bambaF01/Mesure-Tension-cable/Dossier_kicad/alim/alim.kicad_pcb

## KiCad design schematic/CPU_board.kicad_sch

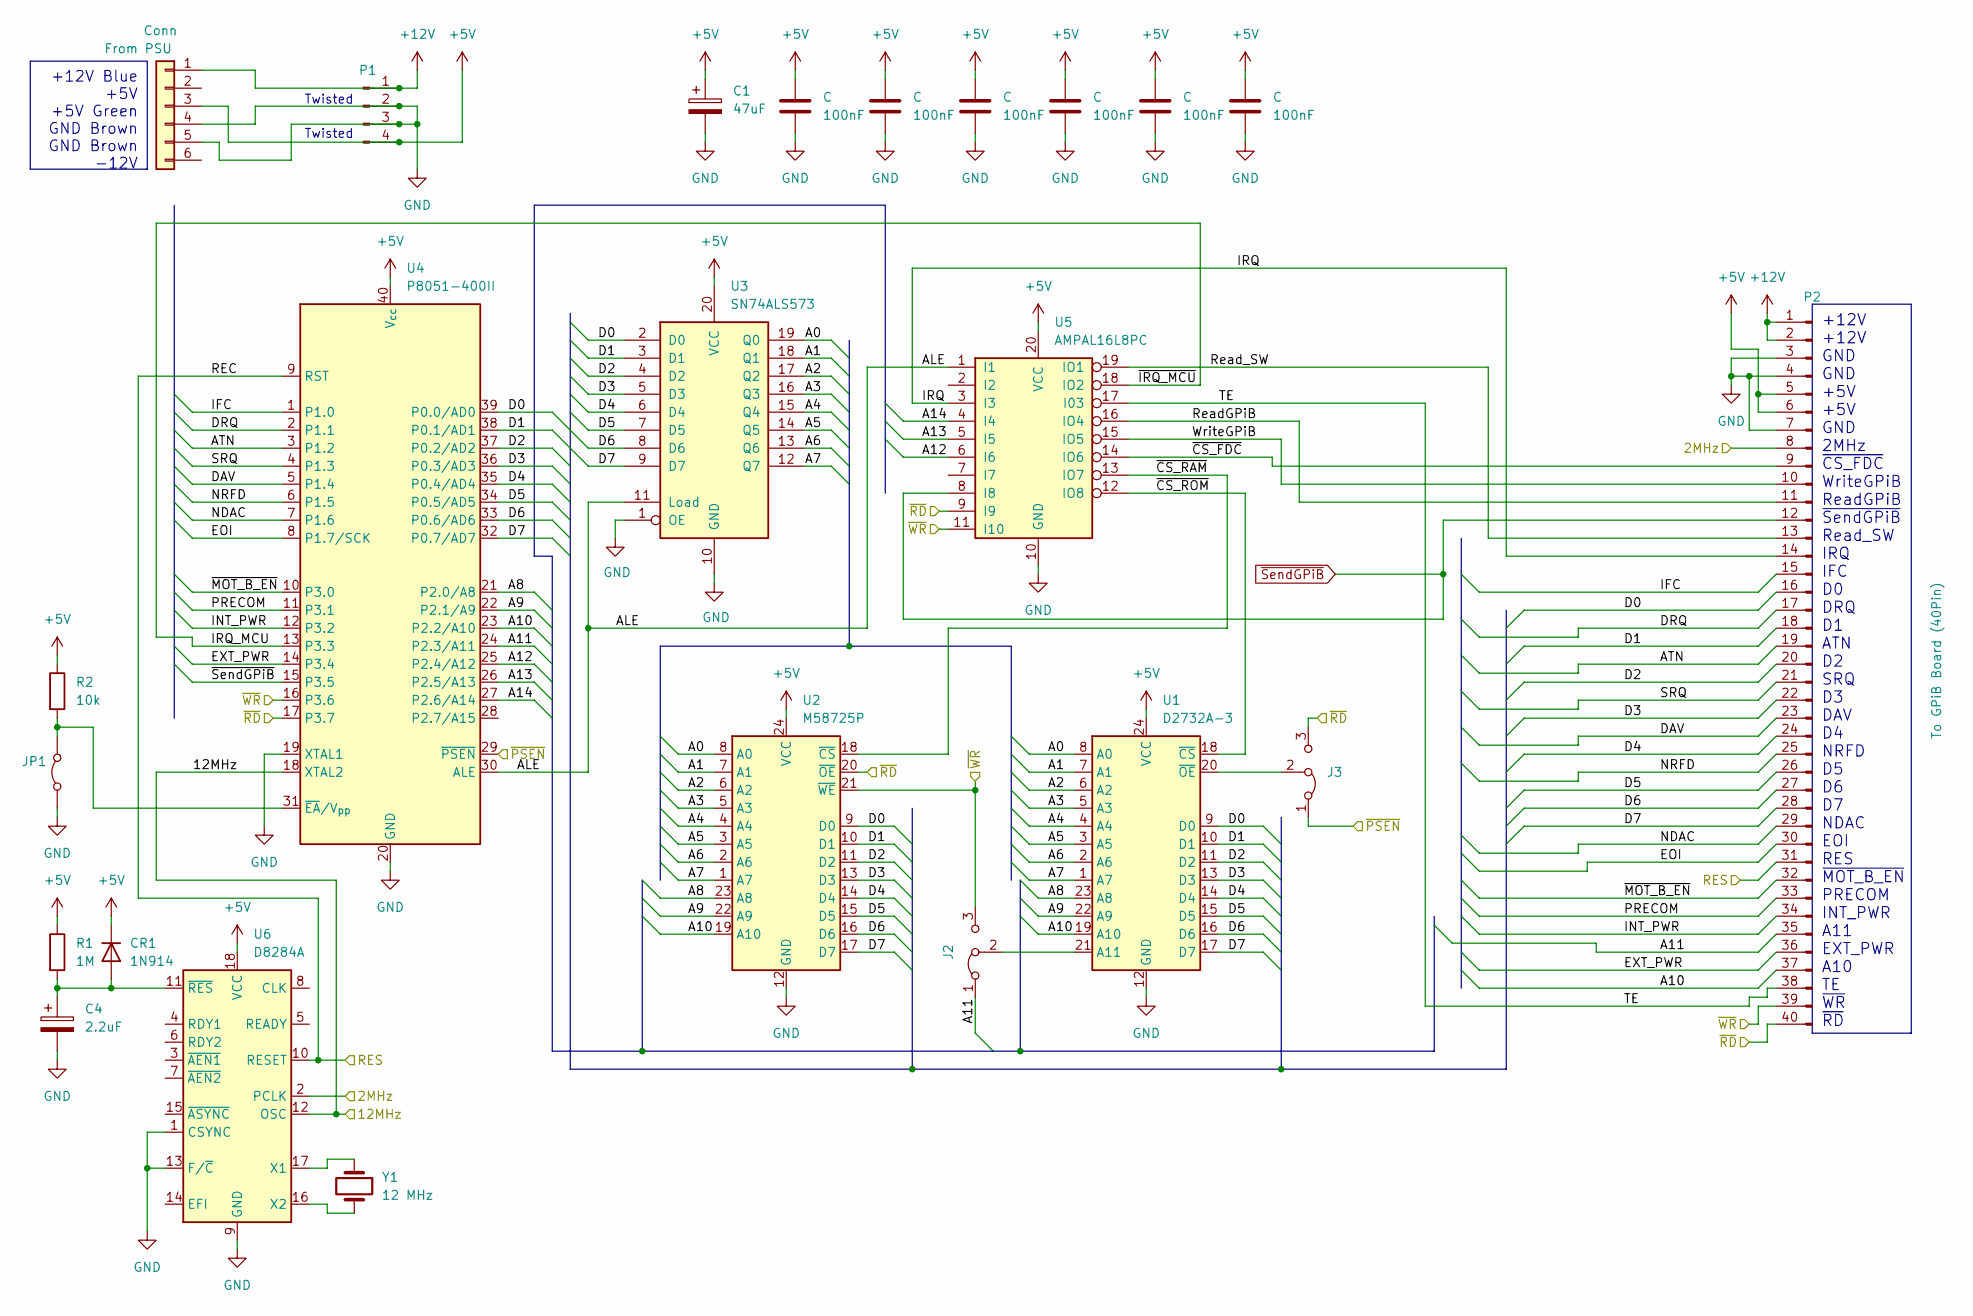
[picture p7: schematic CPU_board.kicad_sch]

Parts:
C: 100nF; C_Disc_D4.3mm_W1.9mm_P5.00mm
C1: 47uF; CP_Axial_L21.0mm_D8.0mm_P28.00mm_Horizontal; Voltage 10V
C4: 2.2uF; C_Disc_D5.0mm_W2.5mm_P2.50mm; Voltage 25V
CR1: 1N914; D_DO-35_SOD27_P10.16mm_Horizontal
Conn: From PSU
J2, J3: Jumper_3_Bridged12
JP1: (no value)
P1: Conn_01x04_Pin
P2: To GPiB Board (40Pin)
R1: 1M; R_Axial_DIN0309_L9.0mm_D3.2mm_P12.70mm_Horizontal
R2: 10k; R_Axial_DIN0309_L9.0mm_D3.2mm_P12.70mm_Horizontal
U1: D2732A-3; DIP-24_W15.24mm
U2: M58725P; DIP-24_W15.24mm
U3: SN74ALS573; DIP-20_W7.62mm
U4: P8051-400II; DIP-40_W15.24mm
U5: AMPAL16L8PC
U6: D8284A; DIP-18_W7.62mm
Y1: 12 MHz; Crystal_HC49-U_Horizontal

Connections:
2MHz: P2.8, U6.2 (PCLK)
12MHz: U4.18 (XTAL2), U6.12 (OSC)
+5V: C.1, C1.1, CR1.1 (K), Conn.3, P1.4, P2.5, P2.6, R1.1, R2.1, U1.24 (VCC), U2.24 (VCC), U3.20 (VCC), U4.40 (V_{cc}), U5.20 (VCC), U6.18 (VCC)
+12V: Conn.1, P1.1, P2.1, P2.2
A0: U1.8 (A0), U2.8 (A0), U3.19 (Q0)
A1: U1.7 (A1), U2.7 (A1), U3.18 (Q1)
A2: U1.6 (A2), U2.6 (A2), U3.17 (Q2)
A3: U1.5 (A3), U2.5 (A3), U3.16 (Q3)
A4: U1.4 (A4), U2.4 (A4), U3.15 (Q4)
A5: U1.3 (A5), U2.3 (A5), U3.14 (Q5)
A6: U1.2 (A6), U2.2 (A6), U3.13 (Q6)
A7: U1.1 (A7), U2.1 (A7), U3.12 (Q7)
A8: U1.23 (A8), U2.23 (A8), U4.21 (P2.0/A8)
A9: U1.22 (A9), U2.22 (A9), U4.22 (P2.1/A9)
A10: U1.19 (A10), U2.19 (A10), U4.23 (P2.2/A10)
A11: J2.1 (A), U4.24 (P2.3/A11)
A12: U4.25 (P2.4/A12), U5.6 (I6)
A13: U4.26 (P2.5/A13), U5.5 (I5)
A14: U4.27 (P2.6/A14), U5.4 (I4)
ALE: U3.11 (Load), U4.30 (ALE), U5.1 (I1)
ATN: U4.3 (P1.2)
D0: U1.9 (D0), U2.9 (D0), U3.2 (D0), U4.39 (P0.0/AD0)
D1: U1.10 (D1), U2.10 (D1), U3.3 (D1), U4.38 (P0.1/AD1)
D2: U1.11 (D2), U2.11 (D2), U3.4 (D2), U4.37 (P0.2/AD2)
D3: U1.13 (D3), U2.13 (D3), U3.5 (D3), U4.36 (P0.3/AD3)
D4: U1.14 (D4), U2.14 (D4), U3.6 (D4), U4.35 (P0.4/AD4)
D5: U1.15 (D5), U2.15 (D5), U3.7 (D5), U4.34 (P0.5/AD5)
D6: U1.16 (D6), U2.16 (D6), U3.8 (D6), U4.33 (P0.6/AD6)
D7: U1.17 (D7), U2.17 (D7), U3.9 (D7), U4.32 (P0.7/AD7)
DAV: U4.5 (P1.4)
DRQ: U4.2 (P1.1)
EOI: U4.8 (P1.7/SCK)
EXT_PWR: U4.14 (P3.4)
GND: C.2, C1.2, C4.2, Conn.4, Conn.5, JP1.1 (A), P1.2, P1.3, P2.3, P2.4, P2.7, U1.12 (GND), U2.12 (GND), U3.1 (OE), U3.10 (GND), U4.19 (XTAL1), U4.20 (GND), U5.10 (GND), U6.1 (CSYNC), U6.9 (GND), U6.13 (F/~C)
IFC: U4.1 (P1.0)
INT_PWR: U4.12 (P3.2)
IRQ: P2.14, U5.3 (I3)
IRQ_MCU: U4.13 (P3.3), U5.18 (IO2)
NDAC: U4.7 (P1.6)
NRFD: U4.6 (P1.5)
unnamed: C4.1, CR1.2 (A), R1.2, U6.11 (~RES)
unnamed: J2.2 (C), U1.21 (A11)
unnamed: J3.2 (C), U1.20 (~OE)
unnamed: JP1.2 (B), R2.2, U4.31 (~EA/V_{pp})
unnamed: U6.16 (X2), Y1.2
unnamed: U6.17 (X1), Y1.1
PRECOM: U4.11 (P3.1)
REC: U4.9 (RST), U6.10 (RESET)
ReadGPiB: P2.11, U5.16 (IO4)
Read_SW: P2.13, U5.19 (IO1)
SRQ: U4.4 (P1.3)
WriteGPiB: P2.10, U5.15 (IO5)
~CS_FDC: P2.9, U5.14 (IO6)
~CS_RAM: U2.18 (~CS), U5.13 (IO7)
~CS_ROM: U1.18 (~CS), U5.12 (IO8)
~MOT_B_EN: U4.10 (P3.0)
~PSEN: J3.1 (A), U4.29 (~PSEN)
~RD: J3.3 (B), P2.40, U2.20 (~OE), U4.17 (P3.7), U5.9 (I9)
~SendGPiB: P2.12, U4.15 (P3.5), U5.8 (I8)
~WR: J2.3 (B), P2.39, U2.21 (~WE), U4.16 (P3.6), U5.11 (I10)
ТЕ: P2.38, U5.17 (I03)

Notes on the sheet:
+12V +12V GND GND +5V +5V GND 2MHz ~{CS_FDC} WriteGPiB ReadGPiB ~{SendGPiB} Read_SW IRQ IFC D0 DRQ D1 ATN D2 SRQ D3 DAV D4 NRFD D5 D6 D7 NDAC EOI RES ~{MOT_B_EN} PRECOM INT_PWR A11 EXT_PWR A10 ТЕ ~{WR} ~{RD}
+12V Blue +5V +5V Green GND Brown GND Brown -12V
Twisted
