bambaF01/Mesure-Tension-cable/Dossier_kicad/alim/alim.kicad_pcb

## KiCad design schematic/GPiB_Board.kicad_sch

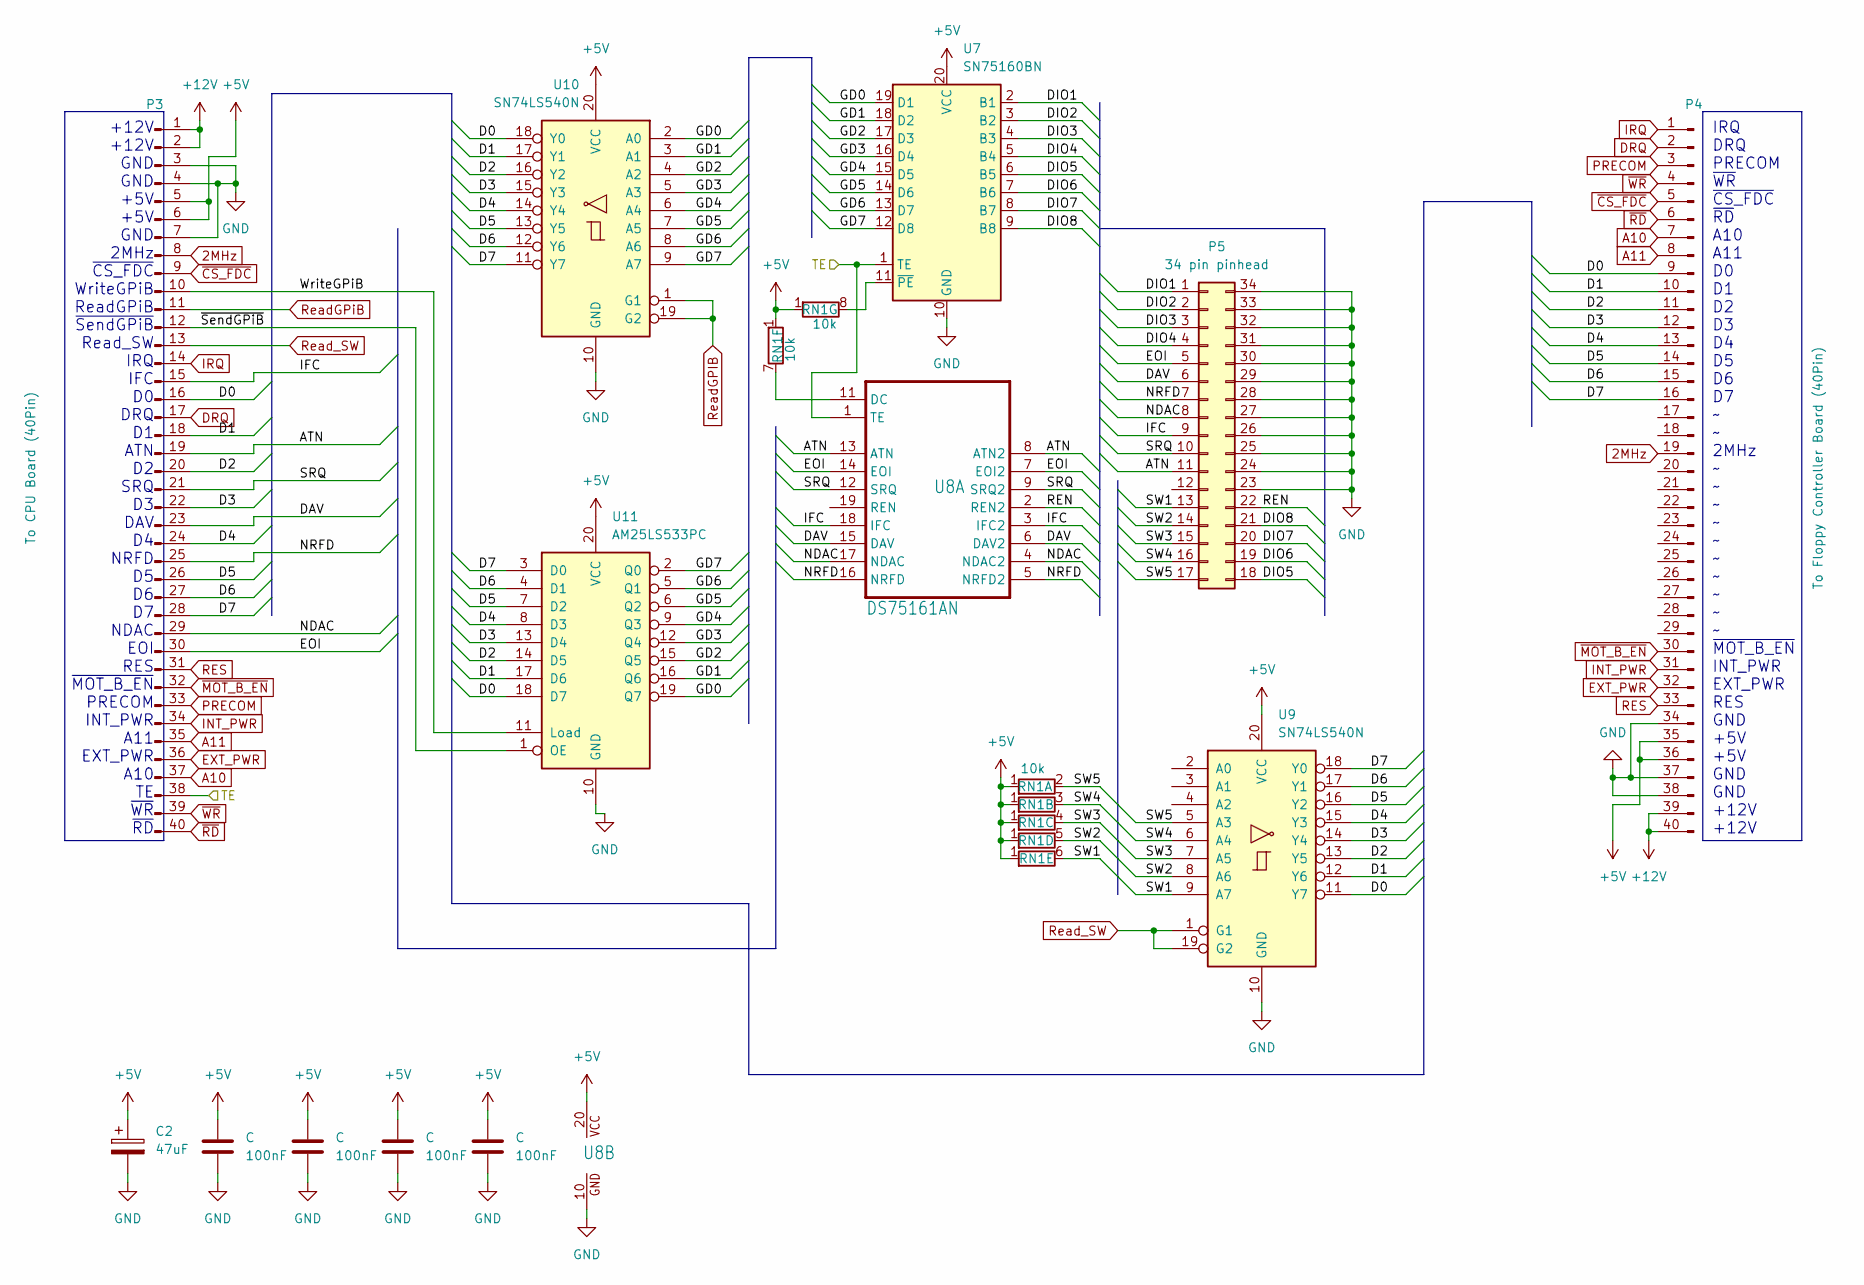
[picture p9: schematic GPiB_Board.kicad_sch]

Parts:
C: 100nF; C_Disc_D4.3mm_W1.9mm_P5.00mm
C2: 47uF; CP_Axial_L21.0mm_D8.0mm_P28.00mm_Horizontal; Voltage 10V
P3: To CPU Board (40Pin)
P4: To Floppy Controller Board (40Pin)
P5: 34 pin pinhead
RN1: 10k; R_Array_SIP8
U7: SN75160BN; DIP-20_W7.62mm
U8: 75161P; DIL20
U9, U10: SN74LS540N
U11: AM25LS533PC

Connections:
2MHz: P3.8, P4.19
+5V: C.1, C2.1, P3.5, P3.6, P4.35, P4.36, RN1.1 (R1), U7.20 (VCC), U8.20 (VCC), U9.20 (VCC), U10.20 (VCC), U11.20 (VCC)
+12V: P3.1, P3.2, P4.39, P4.40
A10: P3.37, P4.7
A11: P3.35, P4.8
ATN: P3.19, P5.11, U8.8 (ATN2), U8.13 (ATN)
D0: P3.16, P4.9, U9.11 (Y7), U10.18 (Y0), U11.18 (D7)
D1: P3.18, P4.10, U9.12 (Y6), U10.17 (Y1), U11.17 (D6)
D2: P3.20, P4.11, U9.13 (Y5), U10.16 (Y2), U11.14 (D5)
D3: P3.22, P4.12, U9.14 (Y4), U10.15 (Y3), U11.13 (D4)
D4: P3.24, P4.13, U9.15 (Y3), U10.14 (Y4), U11.8 (D3)
D5: P3.26, P4.14, U9.16 (Y2), U10.13 (Y5), U11.7 (D2)
D6: P3.27, P4.15, U9.17 (Y1), U10.12 (Y6), U11.4 (D1)
D7: P3.28, P4.16, U9.18 (Y0), U10.11 (Y7), U11.3 (D0)
DAV: P3.23, P5.6, U8.6 (DAV2), U8.15 (DAV)
DIO1: P5.1, U7.2 (B1)
DIO2: P5.2, U7.3 (B2)
DIO3: P5.3, U7.4 (B3)
DIO4: P5.4, U7.5 (B4)
DIO5: P5.18, U7.6 (B5)
DIO6: P5.19, U7.7 (B6)
DIO7: P5.20, U7.8 (B7)
DIO8: P5.21, U7.9 (B8)
DRQ: P3.17, P4.2
EOI: P3.30, P5.5, U8.7 (EOI2), U8.14 (EOI)
EXT_PWR: P3.36, P4.32
GD0: U7.19 (D1), U10.2 (A0), U11.19 (Q7)
GD1: U7.18 (D2), U10.3 (A1), U11.16 (Q6)
GD2: U7.17 (D3), U10.4 (A2), U11.15 (Q5)
GD3: U7.16 (D4), U10.5 (A3), U11.12 (Q4)
GD4: U7.15 (D5), U10.6 (A4), U11.9 (Q3)
GD5: U7.14 (D6), U10.7 (A5), U11.6 (Q2)
GD6: U7.13 (D7), U10.8 (A6), U11.5 (Q1)
GD7: U7.12 (D8), U10.9 (A7), U11.2 (Q0)
GND: C.2, C2.2, P3.3, P3.4, P3.7, P4.34, P4.37, P4.38, P5.23, P5.24, P5.25, P5.26, P5.27, P5.28, P5.29, P5.30, P5.31, P5.32, P5.33, P5.34, U7.10 (GND), U8.10 (GND), U9.10 (GND), U10.10 (GND), U11.10 (GND)
IFC: P3.15, P5.9, U8.3 (IFC2), U8.18 (IFC)
INT_PWR: P3.34, P4.31
IRQ: P3.14, P4.1
NDAC: P3.29, P5.8, U8.4 (NDAC2), U8.17 (NDAC)
NRFD: P3.25, P5.7, U8.5 (NRFD2), U8.16 (NRFD)
unnamed: RN1.7 (R6.2), U8.11 (DC)
unnamed: RN1.8 (R7.2), U7.11 (~PE)
PRECOM: P3.33, P4.3
REN: P5.22, U8.2 (REN2)
RES: P3.31, P4.33
ReadGPiB: P3.11, U10.1 (G1), U10.19 (G2)
Read_SW: P3.13, U9.1 (G1), U9.19 (G2)
SRQ: P3.21, P5.10, U8.9 (SRQ2), U8.12 (SRQ)
SW1: P5.13, RN1.6 (R5.2), U9.9 (A7)
SW2: P5.14, RN1.5 (R4.2), U9.8 (A6)
SW3: P5.15, RN1.4 (R3.2), U9.7 (A5)
SW4: P5.16, RN1.3 (R2.2), U9.6 (A4)
SW5: P5.17, RN1.2 (R1.2), U9.5 (A3)
WriteGPiB: P3.10, U11.11 (Load)
~CS_FDC: P3.9, P4.5
~MOT_B_EN: P3.32, P4.30
~RD: P3.40, P4.6
~SendGPiB: P3.12, U11.1 (OE)
~WR: P3.39, P4.4
ТЕ: P3.38, U7.1 (TE), U8.1 (TE)

Notes on the sheet:
+12V +12V GND GND +5V +5V GND 2MHz ~{CS_FDC} WriteGPiB ReadGPiB ~{SendGPiB} Read_SW IRQ IFC D0 DRQ D1 ATN D2 SRQ D3 DAV D4 NRFD D5 D6 D7 NDAC EOI RES ~{MOT_B_EN} PRECOM INT_PWR A11 EXT_PWR A10 ТЕ ~{WR} ~{RD}
IRQ DRQ PRECOM ~{WR} ~{CS_FDC} ~{RD} A10 A11 D0 D1 D2 D3 D4 D5 D6 D7 ~ ~ 2MHz ~ ~ ~ ~ ~ ~ ~ ~ ~ ~ ~{MOT_B_EN} INT_PWR EXT_PWR RES GND +5V +5V GND GND +12V +12V
