bambaF01/Mesure-Tension-cable/Dossier_kicad/alim/alim.kicad_pcb

## KiCad design schematic/PSU.kicad_sch

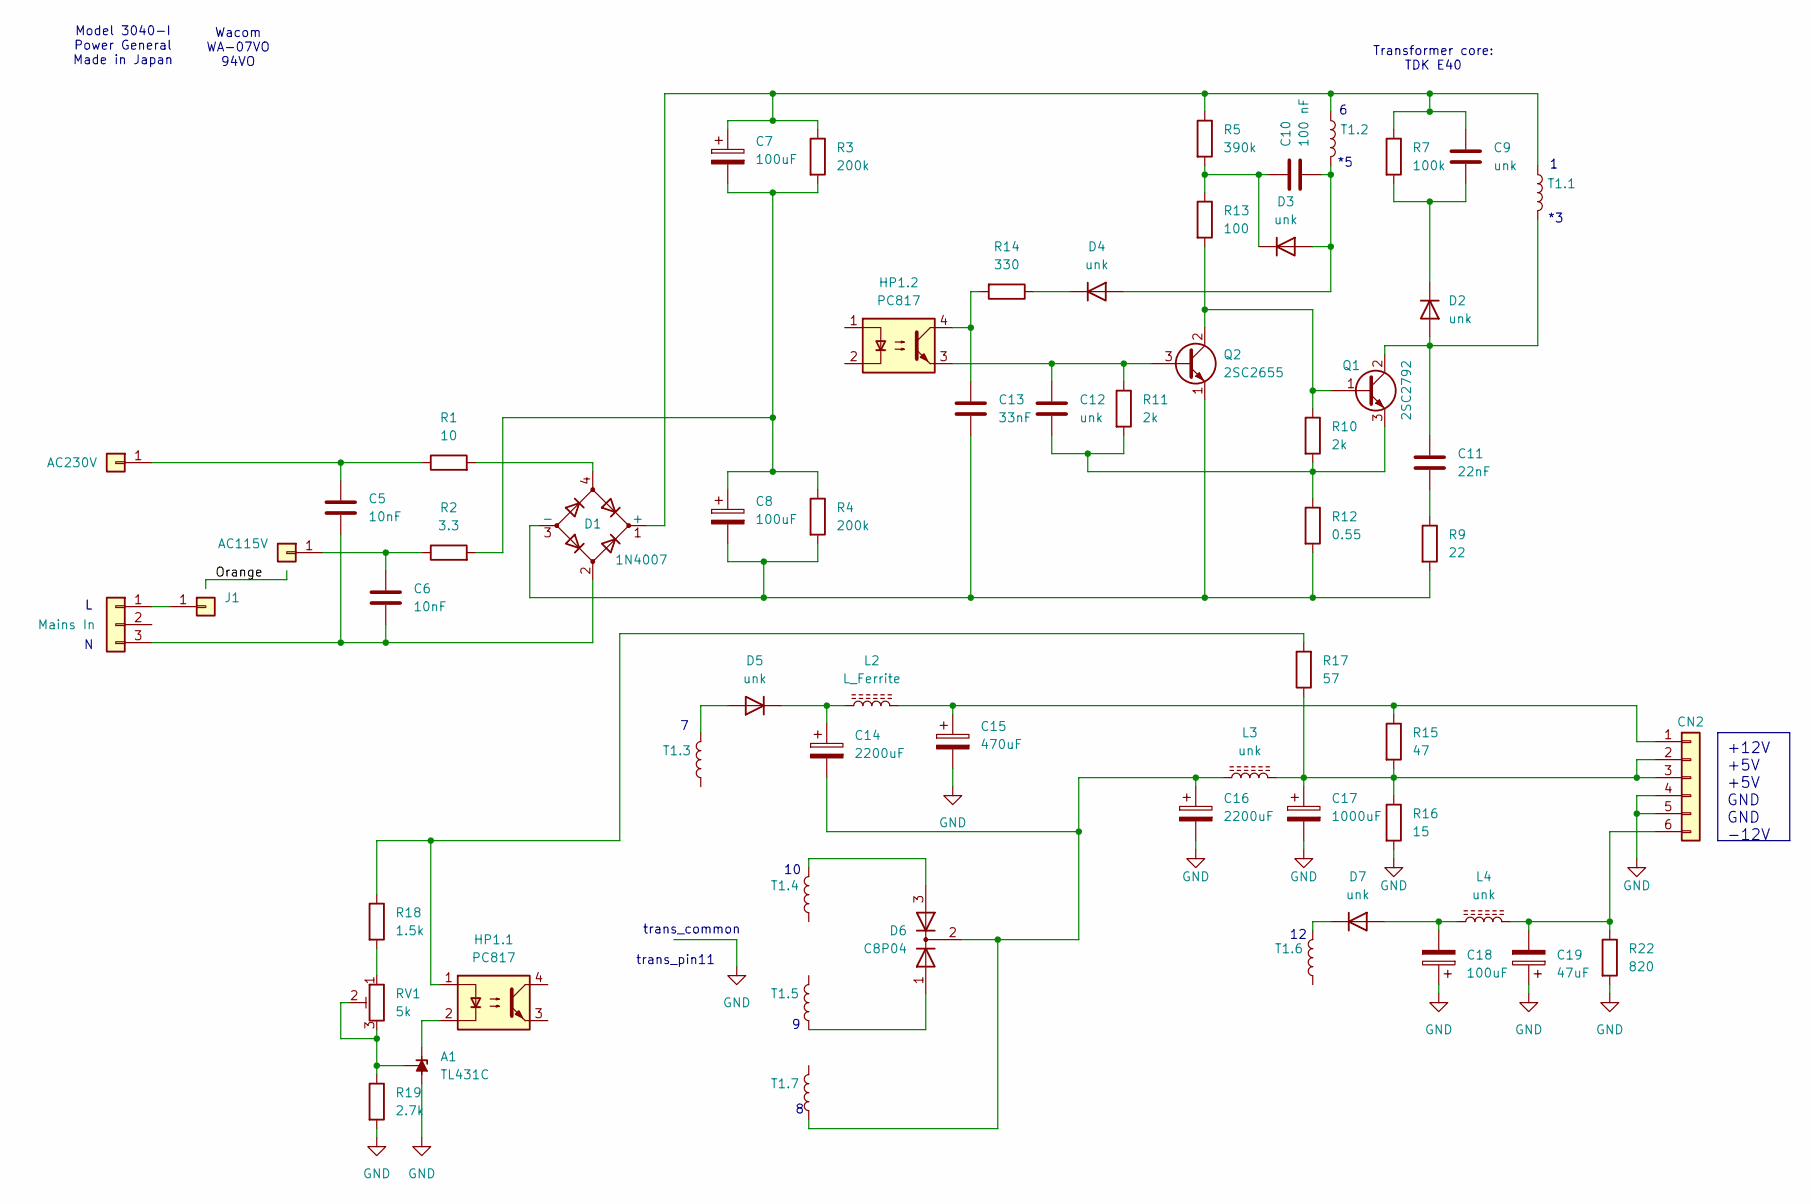
[picture p11: schematic PSU.kicad_sch]

Parts:
A1: TL431C; TO-92_Inline
AC115V: (no value)
C5, C6: 10nF; C_Rect_L10.0mm_W2.5mm_P7.50mm_MKS4; Voltage 630V
C7, C8: 100uF; CP_Radial_D18.0mm_P7.50mm; Voltage 200V
C9, C12: unk; C_Rect_L10.0mm_W2.5mm_P7.50mm_MKS4
C10: 100 nF; C_Rect_L10.0mm_W2.5mm_P7.50mm_MKS4; Voltage 25V
C11: 22nF; C_Rect_L10.0mm_W2.5mm_P7.50mm_MKS4; Voltage 1kV
C13: 33nF; C_Rect_L10.0mm_W2.5mm_P7.50mm_MKS4
C14, C16: 2200uF; CP_Radial_D18.0mm_P7.50mm; Voltage 16V
C15: 470uF; CP_Radial_D18.0mm_P7.50mm; Voltage 25V
C17: 1000uF; CP_Radial_D18.0mm_P7.50mm; Voltage 16V
C18: 100uF; CP_Radial_D18.0mm_P7.50mm; Voltage 25V
C19: 47uF; CP_Radial_D18.0mm_P7.50mm; Voltage 25V
CN1: Mains In; JST_VH_B3P-VH-B_1x03_P3.96mm_Vertical
CN2: Conn_01x06; JST_VH_B6P-VH-B_1x06_P3.96mm_Vertical
D1: 1N4007
D2, D3, D4, D7: unk
D5: unk; D_P600_R-6_P7.62mm_Vertical_KathodeUp
D6: C8P04; TO-220-3_Vertical
HP1.1, HP1.2: PC817; DIP-4_W7.62mm
J1: (no value)
J9: AC230V
L2: L_Ferrite; L_6.3x6.3_H3
L3: unk; L_6.3x6.3_H3
L4: unk
Q1: 2SC2792; TO-3PB-3_Horizontal_TabDown
Q2: 2SC2655; TO-92MOD
R1: 10; R_Radial_Power_L7.0mm_W8.0mm_Px2.40mm_Py2.30mm
R2: 3.3; R_Radial_Power_L7.0mm_W8.0mm_Px2.40mm_Py2.30mm
R3, R4: 200k; R_Axial_DIN0411_L9.9mm_D3.6mm_P7.62mm_Vertical; Tolerance 5%
R5: 390k; R_Axial_Power_L25.0mm_W6.4mm_P27.94mm
R7: 100k; R_Axial_DIN0411_L9.9mm_D3.6mm_P7.62mm_Vertical; Tolerance 5%
R9: 22; R_Axial_Power_L25.0mm_W6.4mm_P27.94mm
R10, R11: 2k; R_Axial_Power_L25.0mm_W6.4mm_P27.94mm; Tolerance 5%
R12: 0.55; R_Axial_DIN0411_L9.9mm_D3.6mm_P7.62mm_Vertical
R13: 100; R_Axial_DIN0411_L9.9mm_D3.6mm_P7.62mm_Vertical; Tolerance 5%
R14: 330; R_Axial_Power_L25.0mm_W6.4mm_P27.94mm
R15: 47; R_Axial_DIN0411_L9.9mm_D3.6mm_P7.62mm_Vertical
R16: 15; R_Axial_DIN0411_L9.9mm_D3.6mm_P7.62mm_Vertical
R17: 57; R_Axial_Power_L25.0mm_W6.4mm_P27.94mm; Tolerance 5%
R18: 1.5k; R_Axial_Power_L25.0mm_W6.4mm_P27.94mm
R19: 2.7k; R_Axial_Power_L25.0mm_W6.4mm_P27.94mm
R22: 820; R_Axial_DIN0411_L9.9mm_D3.6mm_P7.62mm_Vertical
RV1: 5k; Potentiometer_Bourns_3339H_Vertical
T1.1, T1.2, T1.3, T1.4, T1.5, T1.6, T1.7: (no value)

Connections:
GND: A1.2 (A), C15.2, C16.2, C17.2, C18.1, C19.1, CN2.4, CN2.5, R16.2, R19.2, R22.2
unnamed: A1.1 (REF), R19.1, RV1.2, RV1.3
unnamed: A1.3 (K), HP1.1.2
unnamed: AC115V.1, C6.1, R2.1
unnamed: C5.1, J9.1, R1.1
unnamed: C5.2, C6.2, CN1.3, D1.2
unnamed: C7.1, C9.1, D1.1 (+), R3.1, R5.1, R7.1, T1.1.1, T1.2.1
unnamed: C7.2, C8.1, R2.2, R3.2, R4.1
unnamed: C9.2, D2.1 (K), R7.2
unnamed: C10.1, D3.1 (K), R5.2, R13.1
unnamed: C10.2, D3.2 (A), D4.2 (A), T1.2.2
unnamed: C11.1, D2.2 (A), Q1.2 (C), T1.1.2
unnamed: C11.2, R9.1
unnamed: C12.1, HP1.2.3, Q2.3 (B), R11.1
unnamed: C12.2, Q1.3 (E), R10.2, R11.2, R12.1
unnamed: C13.1, HP1.2.4, R14.2
unnamed: C8.2, C13.2, D1.3 (-), Q2.1 (E), R4.2, R9.2, R12.2
unnamed: C14.1, D5.1 (K), L2.1
unnamed: C14.2, C16.1, D6.2 (K), L3.1, T1.7.2
unnamed: C15.1, CN2.1, L2.2, R15.1
unnamed: C17.1, CN2.2, CN2.3, L3.2, R15.2, R16.1, R17.1
unnamed: C18.2, D7.2 (A), L4.1
unnamed: C19.2, CN2.6, L4.2, R22.1
unnamed: CN1.1, J1.1
unnamed: D1.4, R1.2
unnamed: D4.1 (K), R14.1
unnamed: D5.2 (A), T1.3.1
unnamed: D6.1 (A), T1.5.2
unnamed: D6.3 (A), T1.4.1
unnamed: D7.1 (K), T1.6.1
unnamed: HP1.1.1, R17.2, R18.1
unnamed: Q1.1 (B), Q2.2 (C), R10.1, R13.2
unnamed: R18.2, RV1.1

Notes on the sheet:
+12V +5V +5V GND GND -12V
trans_pin11
Transformer core: TDK E40
Wacom WA-07VO 94VO
Model 3040-I Power General Made in Japan
trans_common
